alksarioglou/embedded_systems_robot_project/Robot_CAD_Models/1.PNG

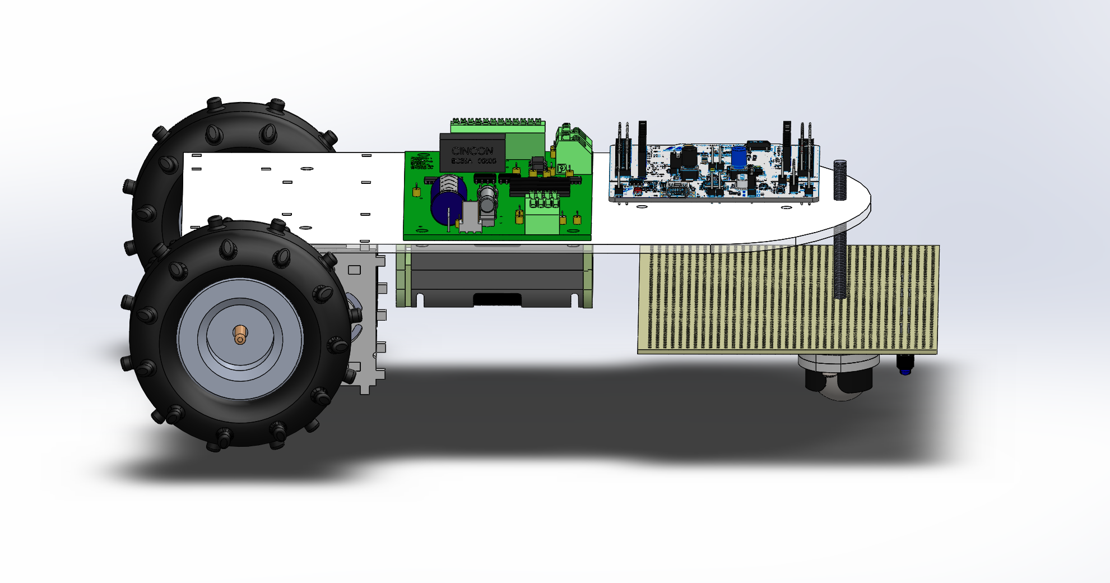
Robot_CAD_Models/1.PNG
