alksarioglou/embedded_systems_robot_project/Robot_CAD_Models/2.PNG

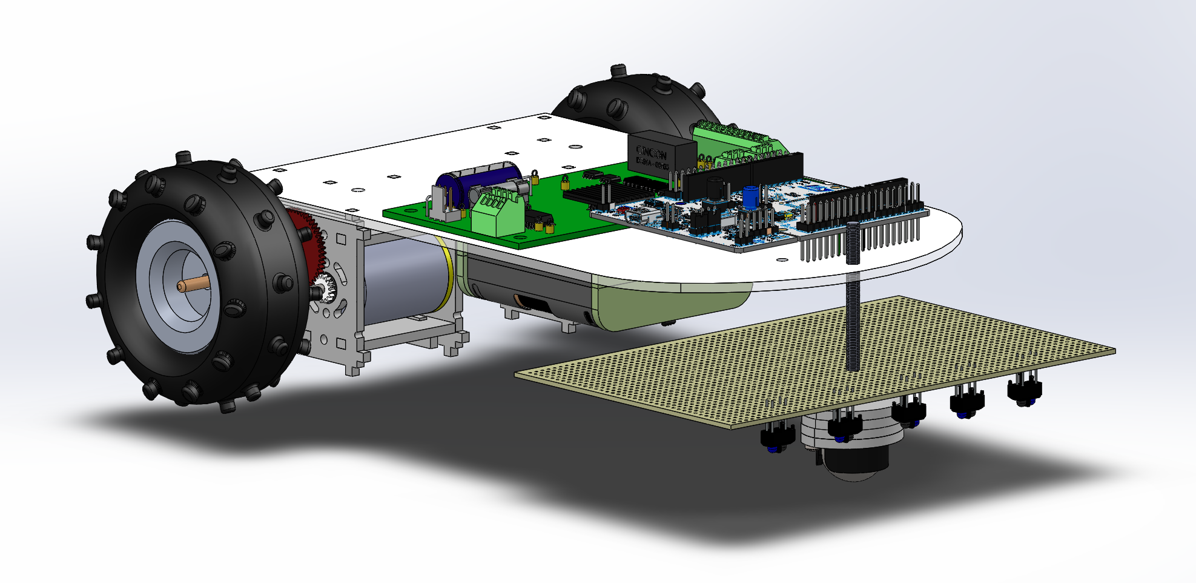
Robot_CAD_Models/2.PNG
