alksarioglou/embedded_systems_robot_project/Robot_CAD_Models/4.PNG

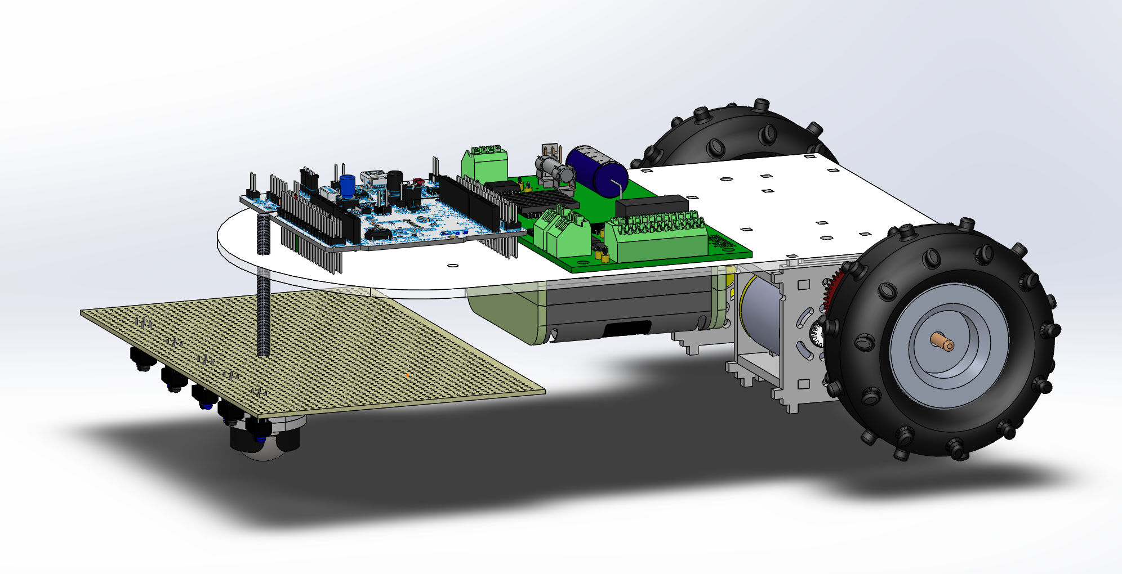
Robot_CAD_Models/4.PNG
