alksarioglou/embedded_systems_robot_project/Robot_CAD_Models/6.PNG

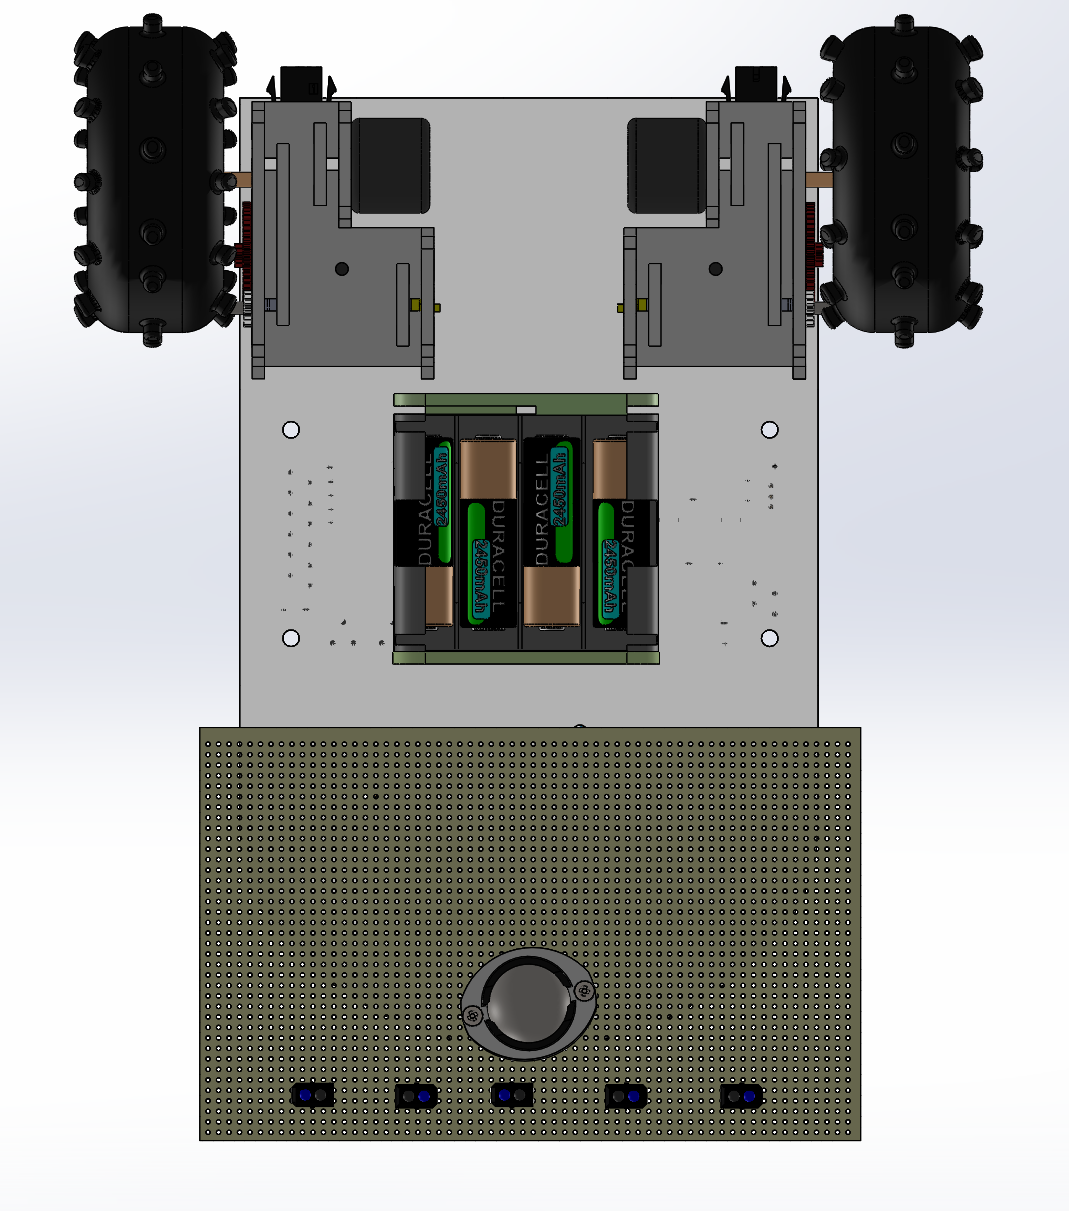
Robot_CAD_Models/6.PNG
